lemosslucas/CoRA2024/data/kp100.00.jpg

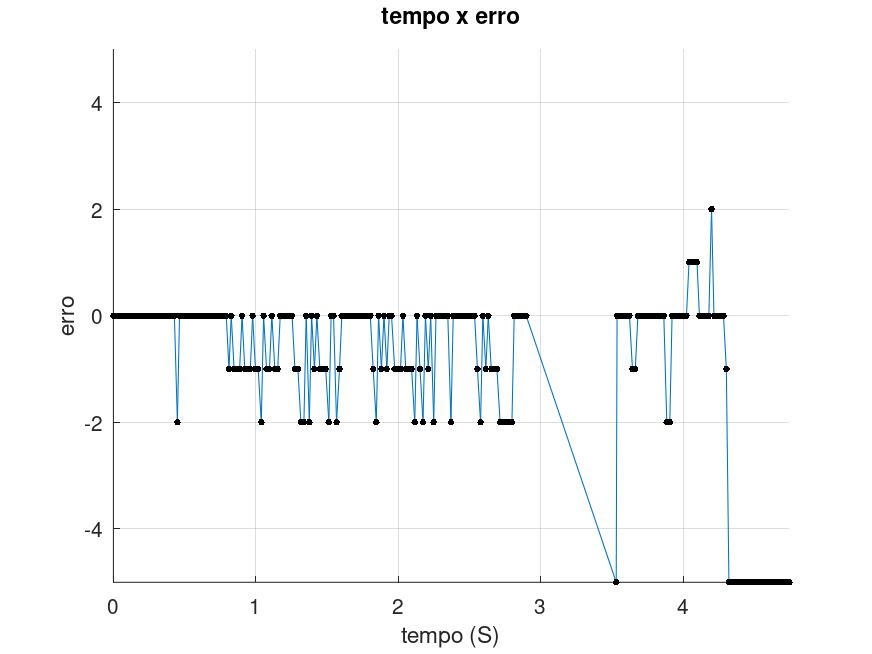
data/kp100.00.jpg
