lemosslucas/CoRA2024/data/kp150.00.jpg

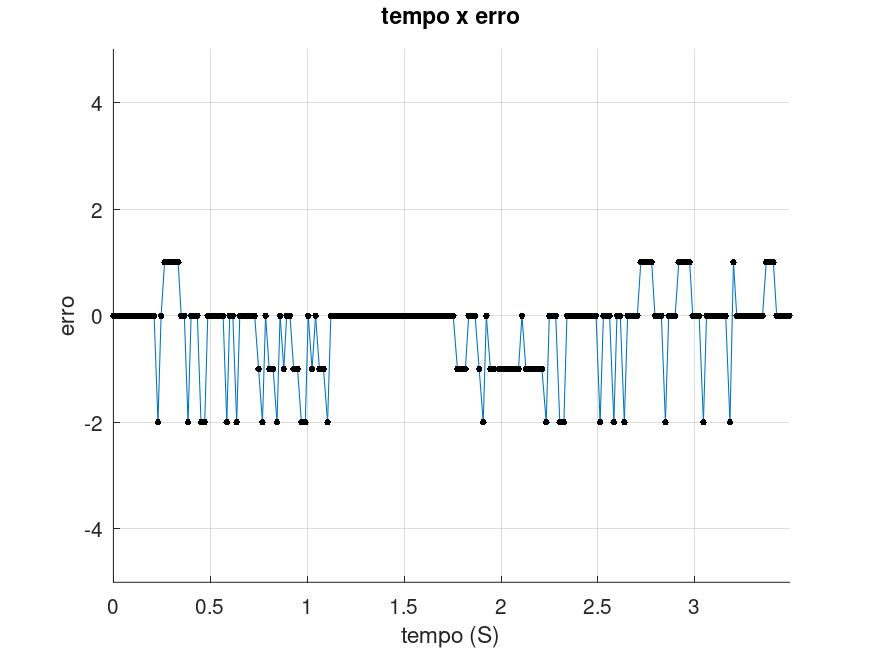
data/kp150.00.jpg
