lemosslucas/CoRA2024/data/kp200.00.jpg

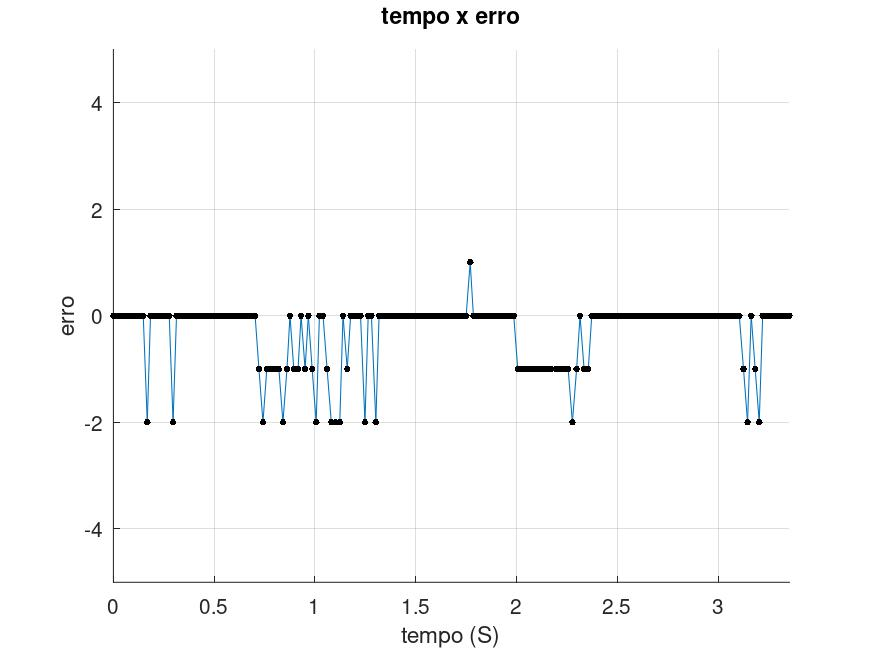
data/kp200.00.jpg
